MehrzadGolabi/selfbalancingrobot/Circuit/pendulumRobotModule.kicad_sch

## KiCad design Circuit/pendulumRobotModule.kicad_sch (2024-07-07)

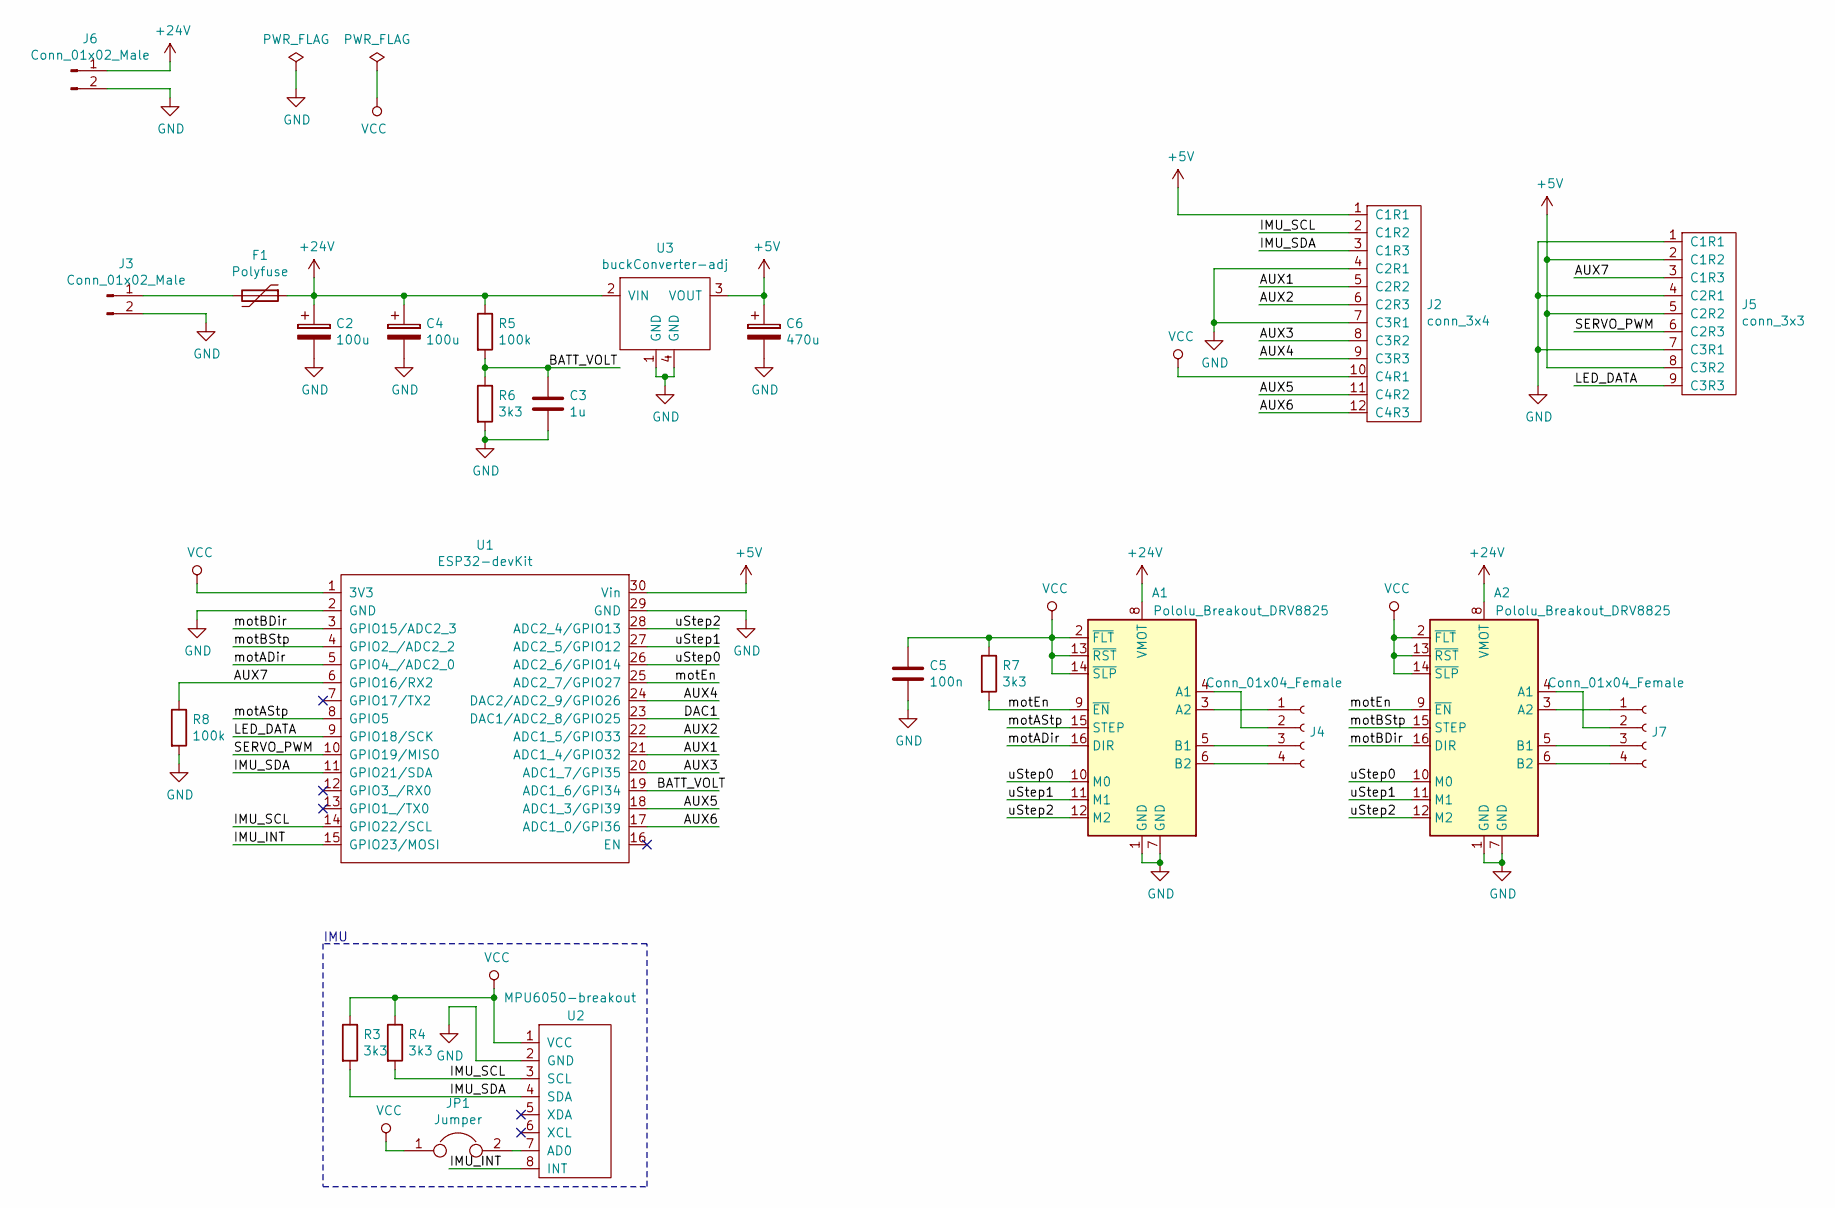
[picture p28: schematic pendulumRobotModule.kicad_sch]

Parts:
A1, A2: Pololu_Breakout_DRV8825; DRV8825-breakout
C2, C4: 100u; CP_Radial_D8.0mm_P2.50mm
C3: 1u; C_0805_HandSoldering
C5: 100n; C_0805_HandSoldering
C6: 470u; CP_Radial_D6.3mm_P2.50mm
F1: Polyfuse; polyfuse-5.08mm
J2: conn_3x4; pinHeader_3x4
J3: Conn_01x02_Male; wirePad-2x-2mm
J4, J7: Conn_01x04_Female; Socket_Strip_Straight_1x04_Pitch2.54mm
J5: conn_3x3; pinHeader_3x3
J6: Conn_01x02_Male; pinHeader_2x1_5.08mm
JP1: Jumper; GS2
R3, R4, R6, R7: 3k3; R_0805_HandSoldering
R5, R8: 100k; R_0805_HandSoldering
U1: ESP32-devKit; ESP32-devkit-30p
U2: MPU6050-breakout; MPU6050-breakout-angledHeader
U3: buckConverter-adj; buck-converter-adj

Connections:
+5V: C6.1, J2.1 (C1R1), J5.2 (C1R2), J5.5 (C2R2), J5.8 (C3R2), U1.30 (Vin), U3.3 (VOUT)
+24V: A1.8 (VMOT), A2.8 (VMOT), C2.1, C4.1, F1.1, J6.1, R5.1, U3.2 (VIN)
AUX1: J2.5 (C2R2), U1.21 (ADC1_4/GPIO32)
AUX2: J2.6 (C2R3), U1.22 (ADC1_5/GPIO33)
AUX3: J2.8 (C3R2), U1.20 (ADC1_7/GPI35)
AUX4: J2.9 (C3R3), U1.24 (DAC2/ADC2_9/GPIO26)
AUX5: J2.11 (C4R2), U1.18 (ADC1_3/GPI39)
AUX6: J2.12 (C4R3), U1.17 (ADC1_0/GPI36)
AUX7: J5.3 (C1R3), R8.1, U1.6 (GPIO16/RX2)
BATT_VOLT: C3.1, R5.2, R6.1, U1.19 (ADC1_6/GPI34)
DAC1: U1.23 (DAC1/ADC2_8/GPIO25)
GND: A1.1 (GND), A1.7 (GND), A2.1 (GND), A2.7 (GND), C2.2, C3.2, C4.2, C5.2, C6.2, J2.4 (C2R1), J2.7 (C3R1), J3.2, J5.1 (C1R1), J5.4 (C2R1), J5.7 (C3R1), J6.2, R6.2, R8.2, U1.2 (GND), U1.29 (GND), U2.2 (GND), U3.1 (GND), U3.4 (GND)
IMU_INT: U1.15 (GPIO23/MOSI), U2.8 (INT)
IMU_SCL: J2.2 (C1R2), R4.2, U1.14 (GPIO22/SCL), U2.3 (SCL)
IMU_SDA: J2.3 (C1R3), R3.2, U1.11 (GPIO21/SDA), U2.4 (SDA)
LED_DATA: J5.9 (C3R3), U1.9 (GPIO18/SCK)
unnamed: A1.3 (A2), J4.1
unnamed: A1.4 (A1), J4.2
unnamed: A1.5 (B1), J4.3
unnamed: A1.6 (B2), J4.4
unnamed: A2.3 (A2), J7.1
unnamed: A2.4 (A1), J7.2
unnamed: A2.5 (B1), J7.3
unnamed: A2.6 (B2), J7.4
unnamed: F1.2, J3.1
unnamed: JP1.2, U2.7 (AD0)
SERVO_PWM: J5.6 (C2R3), U1.10 (GPIO19/MISO)
VCC: A1.2 (~FLT), A1.13 (~RST), A1.14 (~SLP), A2.2 (~FLT), A2.13 (~RST), A2.14 (~SLP), C5.1, J2.10 (C4R1), JP1.1, R3.1, R4.1, R7.1, U1.1 (3V3), U2.1 (VCC)
motADir: A1.16 (DIR), U1.5 (GPIO4_/ADC2_0)
motAStp: A1.15 (STEP), U1.8 (GPIO5)
motBDir: A2.16 (DIR), U1.3 (GPIO15/ADC2_3)
motBStp: A2.15 (STEP), U1.4 (GPIO2_/ADC2_2)
motEn: A1.9 (~EN), A2.9 (~EN), R7.2, U1.25 (ADC2_7/GPIO27)
uStep0: A1.10 (M0), A2.10 (M0), U1.26 (ADC2_6/GPIO14)
uStep1: A1.11 (M1), A2.11 (M1), U1.27 (ADC2_5/GPIO12)
uStep2: A1.12 (M2), A2.12 (M2), U1.28 (ADC2_4/GPIO13)

Notes on the sheet:
IMU
